Zabauski/Blood-Oxygen-and-Heart-Rate-Monitoring-System/electrical-schematics/schematic.kicad_sch

## KiCad design electrical-schematics/schematic.kicad_sch (2025-05-17)

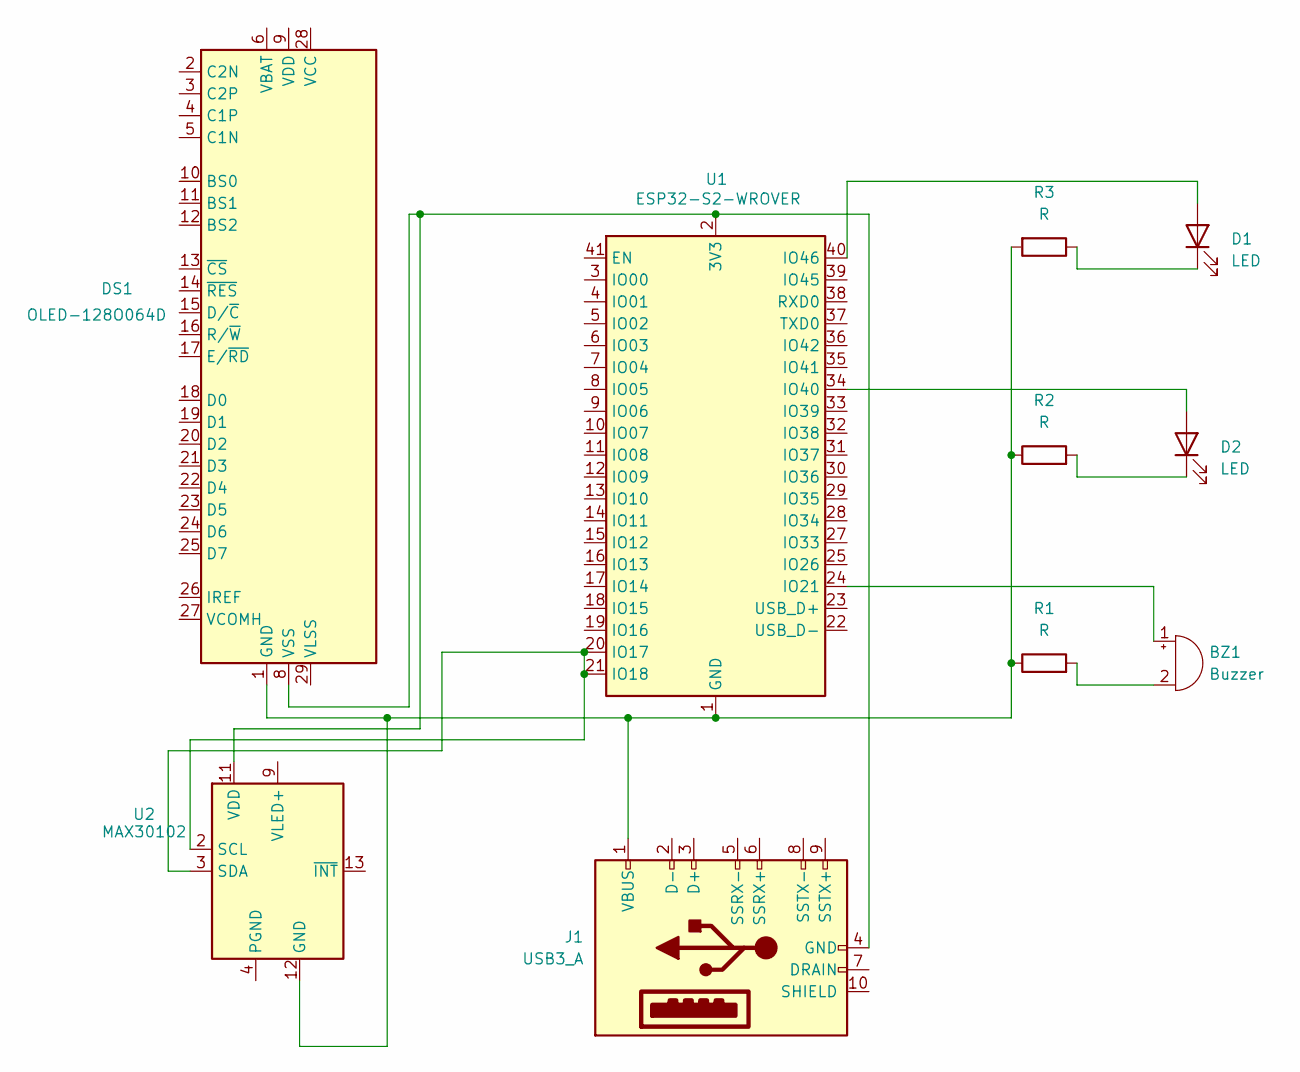
[picture p15: schematic schematic.kicad_sch]

Parts:
BZ1: Buzzer
D1, D2: LED
DS1: OLED-128O064D
J1: USB3_A
R1, R2, R3: R
U1: ESP32-S2-WROVER
U2: MAX30102; Maxim_OLGA-14_3.3x5.6mm_P0.8mm

Connections:
unnamed: BZ1.1 (+), U1.24 (IO21)
unnamed: BZ1.2 (-), R1.2
unnamed: D1.1 (K), R3.1
unnamed: D1.2 (A), U1.40 (IO46)
unnamed: D2.1 (K), R2.2
unnamed: D2.2 (A), U1.34 (IO40)
unnamed: DS1.1 (GND), DS1.30 (GND), J1.1 (VBUS), R1.1, R2.1, R3.2, U1.1 (GND), U1.26 (GND), U1.42 (GND), U1.43 (GND), U2.12 (GND)
unnamed: DS1.8 (VSS), J1.4 (GND), U1.2 (3V3), U2.11 (VDD)
unnamed: U1.20 (IO17), U1.21 (IO18), U2.2 (SCL), U2.3 (SDA)
unnamed: U2.9 (VLED+), U2.10 (VLED+)
